bvernoux/EMC_5uH_LISN/Simu/10dBAttenuator_TransientLimiter.asc

C13: cap; {mc(470.00n, tolC)}
C14: cap; {mc(470.00n, tolC)}
D1: diode; 1N4148
D2: diode; 1N4148
D3: diode; 1N4148
D4: diode; 1N4148
L10: ind; {mc(1.00m, tolL)}; Rser=29
R1: res; 909; tol=1
R2: res; 825; tol=1
R3: res; 12.1; tol=1
R4: res; 243; tol=1
R5: res; 274; tol=1
R6: res; 30.1; tol=1
R7: res; 432; tol=1
R8: res; 432; tol=1
R9: res; 432; tol=1
R10: res; 432; tol=1
R11: res; 18.2; tol=1
R12: res; 562; tol=1
R13: res; 619; tol=1
RL: res; 50
V1: voltage; ""; AC 1 0; Rser=50.00
Named nets: 0
.ac dec 1001 0.001Meg 300.0Meg
.net I(RL) V1
.param tolC=0.1 tolL=0.1
.step param run 1 100 1
